Mandred009/CERBRUS-OpenSource-Quadruped/sensor_suite_arduino/additional_pins.cpp

// Add your additional pins or sensor information here
#include "additional_pins.h"



void init_additional(){

  pinMode(BLUE_LIGHT,OUTPUT);
  pinMode(GREEN_LIGHT,OUTPUT);
  pinMode(LASER,OUTPUT);
  
}
