Mandred009/CERBRUS-OpenSource-Quadruped/sensor_suite_arduino/additional_pins.h

// Add your additional pins or sensor information here
#ifndef ADDITIONAL_H
#define ADDITIONAL_H

#include "Arduino.h"

#define BLUE_LIGHT 32
#define GREEN_LIGHT 31
#define LASER 30

#define BUZZER 33

void init_additional();
void start_tune();


#endif
